eshazen/epic-hours/parts/3digit_screenshot.png

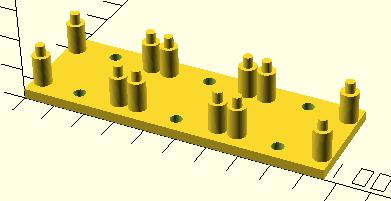
parts/3digit_screenshot.png
