eshazen/epic-hours/parts/#arduino_box_all.dxf

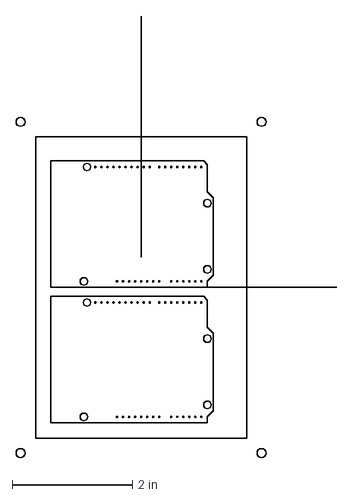
[picture p22: CAD file, 2024-07-11]
parts/#arduino_box_all.dxf
5.33 x 7.33 in
