eshazen/epic-hours/parts/rpi_model/Female USB Type C Connector, RPi4ModelB.SLDPRT

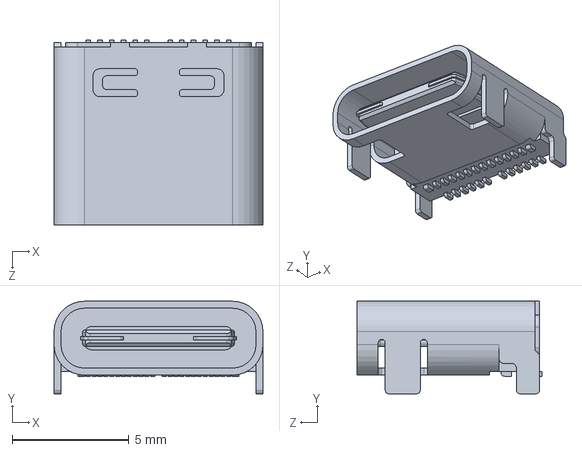
[picture p23: CAD file, 2025-08-05]
parts/rpi_model/Female USB Type C Connector, RPi4ModelB.SLDPRT
8.94 x 3.96 x 7.90 mm
