eshazen/epic-hours/Sketches/cut_back_holes.dxf

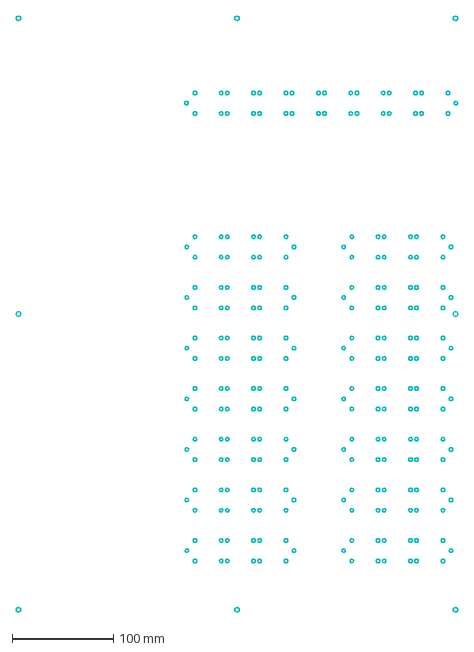
[picture p24: CAD file, 2024-03-23]
Sketches/cut_back_holes.dxf
436.3 x 588.7 mm
