eshazen/epic-hours/parts/arduino_box_cutout.dxf

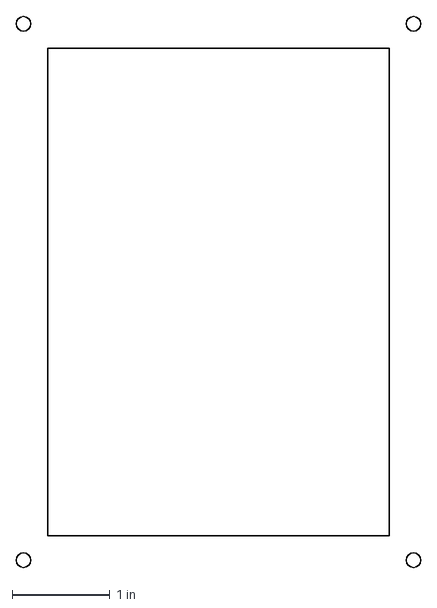
[picture p25: CAD file, 2024-07-11]
parts/arduino_box_cutout.dxf
4.15 x 5.65 in
