eshazen/epic-hours/Sketches/layout_8x8.dxf

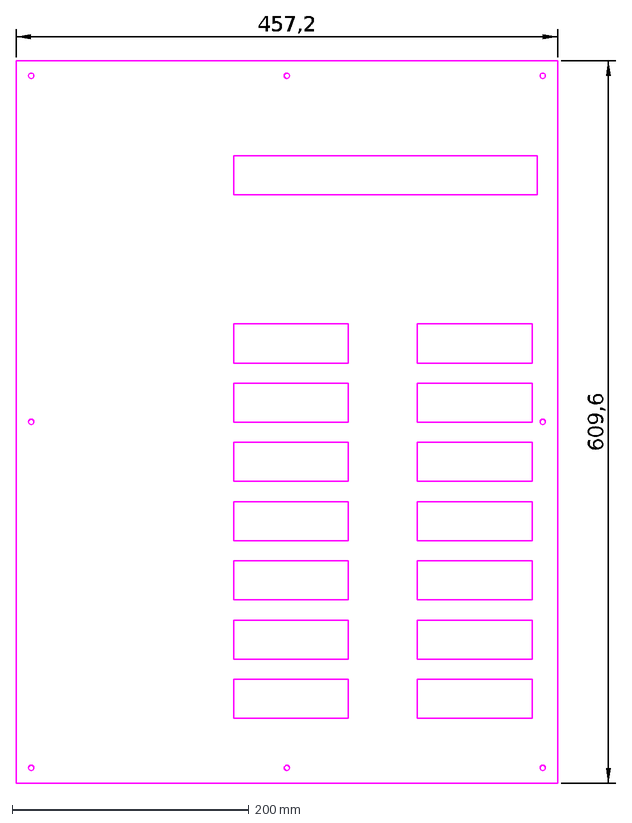
[picture p27: CAD file, 2024-03-07]
Sketches/layout_8x8.dxf
457,2
609,6
