eshazen/epic-hours/parts/arduino_box.stl

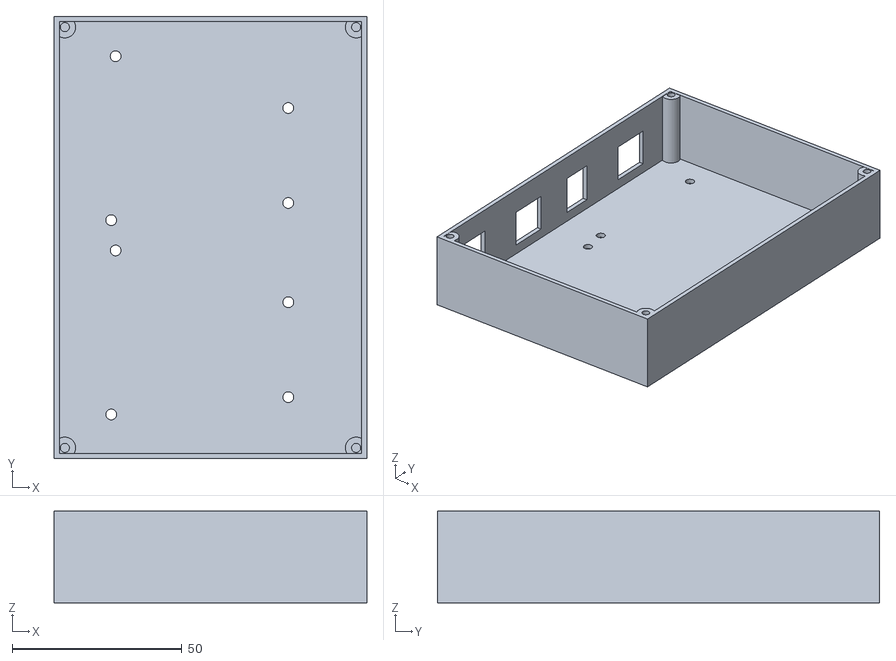
[picture p28: CAD file, 2024-07-11]
parts/arduino_box.stl
92.1 x 130.2 x 27.0
