eshazen/epic-hours/parts/rpi_model/2X USB3.0 PORTS, RPi4ModelB.SLDPRT

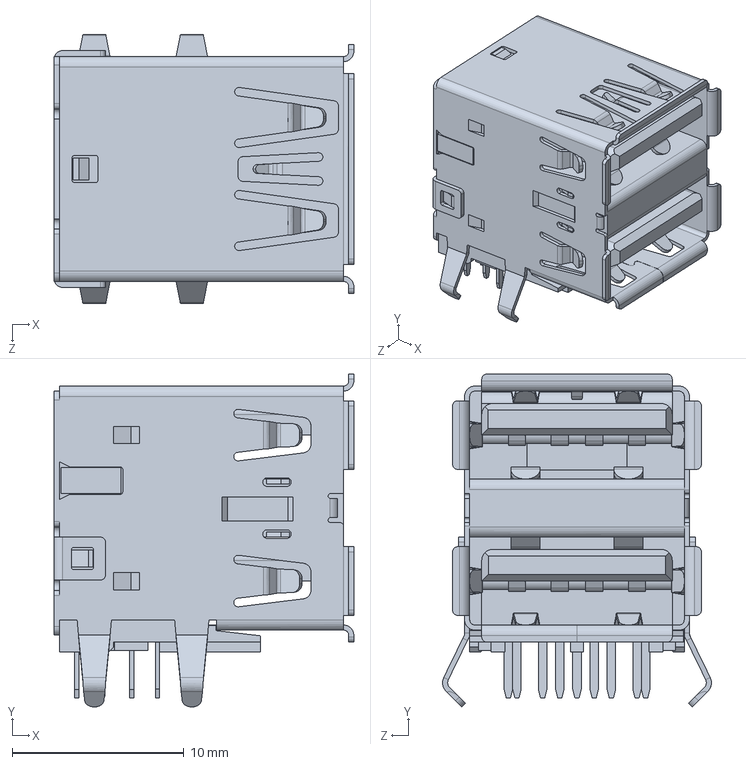
[picture p29: CAD file, 2025-08-05]
parts/rpi_model/2X USB3.0 PORTS, RPi4ModelB.SLDPRT
17.5 x 19.4 x 15.7 mm
