eshazen/epic-hours/Sketches/front_panel.dxf

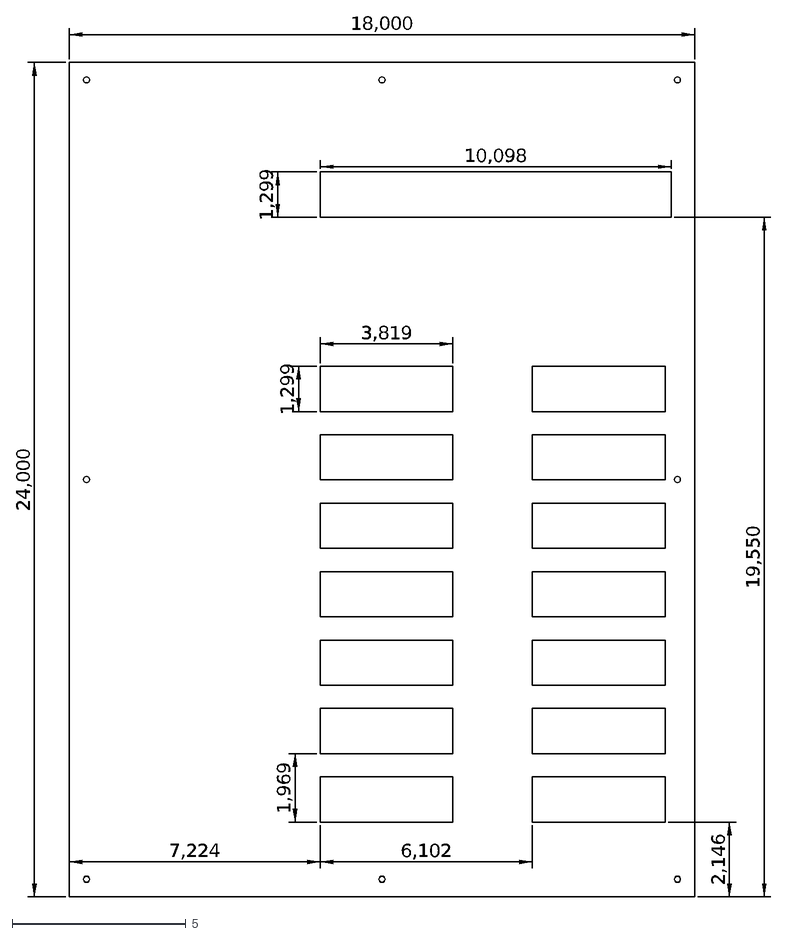
[picture p30: CAD file, 2024-03-07]
Sketches/front_panel.dxf
18,000
3,819
1,299
1,969
6,102
7,224
2,146
24,000
19,550
10,098
