eshazen/epic-hours/parts/arduino_outline.dxf

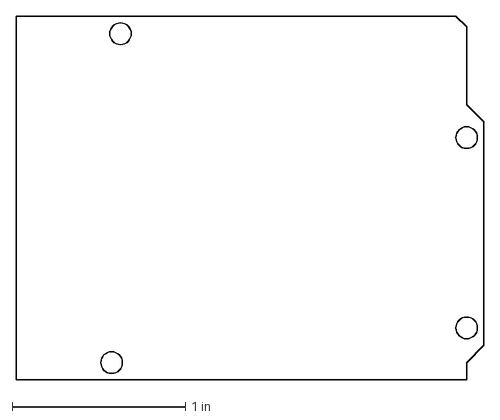
[picture p31: CAD file, 2024-07-11]
parts/arduino_outline.dxf
2.70 x 2.10 in
