eshazen/epic-hours/parts/rpi_model/VIA VL805 PCIe USB 3.0 controller, RPi4ModelB.SLDPRT

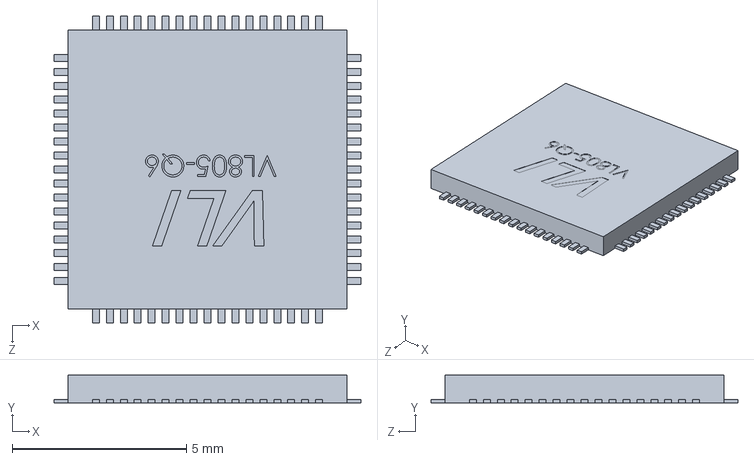
[picture p32: CAD file, 2025-08-05]
parts/rpi_model/VIA VL805 PCIe USB 3.0 controller, RPi4ModelB.SLDPRT
8.80 x 0.8 x 8.80 mm
