eshazen/epic-hours/Sketches/7seg_digit.dxf

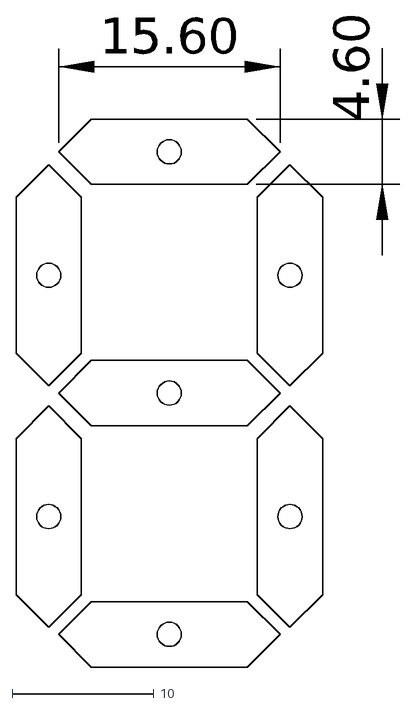
[picture p33: CAD file, 2024-02-12]
Sketches/7seg_digit.dxf
15.60
4.60
