eshazen/epic-hours/parts/8display_standoffs.stl

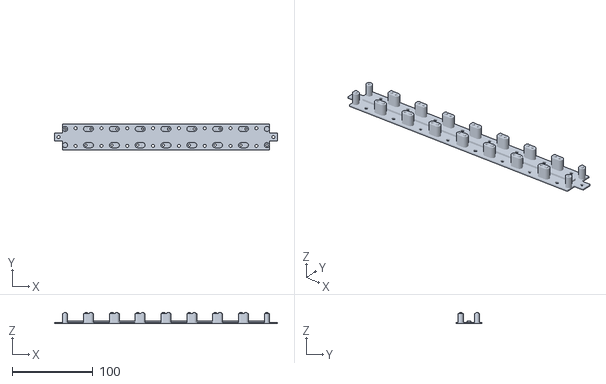
[picture p34: CAD file, 2024-05-08]
parts/8display_standoffs.stl
276.3 x 32.1 x 14.2
