eshazen/epic-hours/parts/rpi_model/2X USB2.0 PORTS, RPi4ModelB.SLDPRT

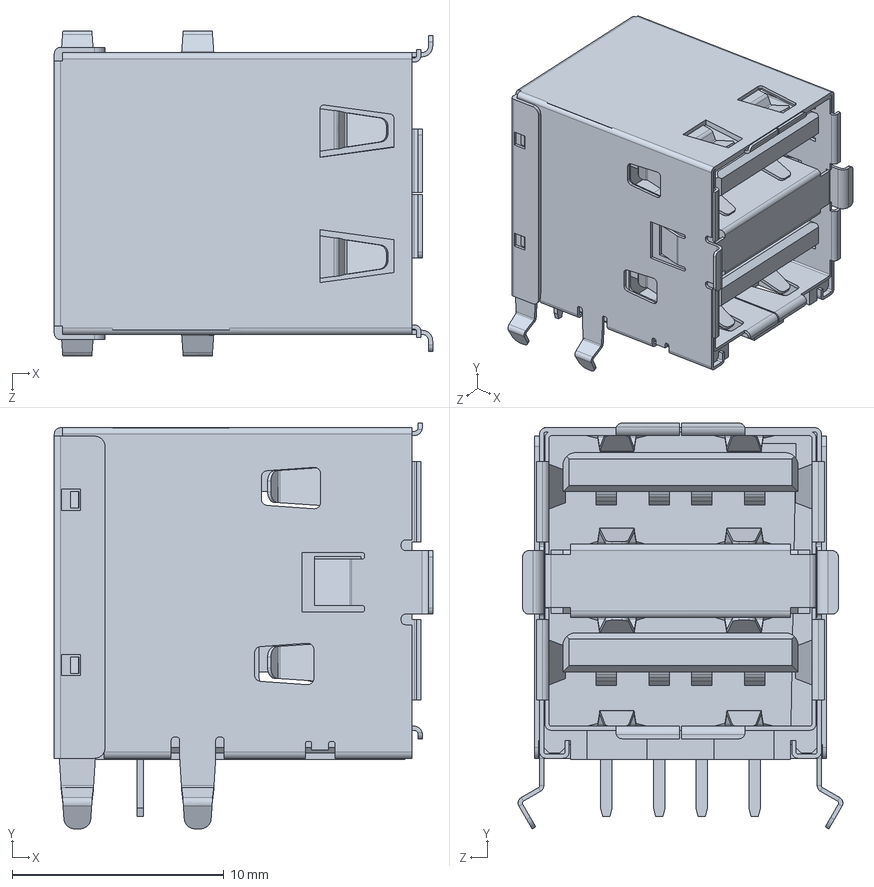
[picture p35: CAD file, 2025-08-05]
parts/rpi_model/2X USB2.0 PORTS, RPi4ModelB.SLDPRT
17.9 x 19.2 x 15.3 mm
