eshazen/epic-hours/parts/display_standoffs.stl

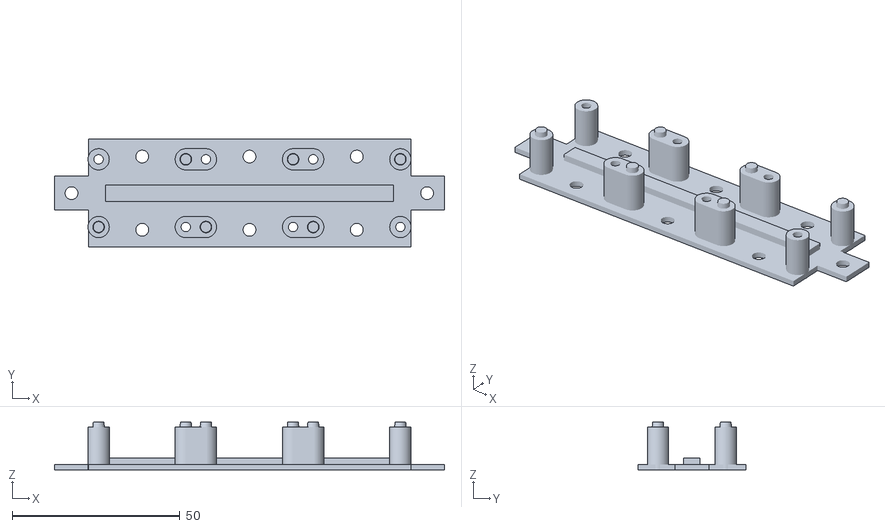
[picture p36: CAD file, 2024-04-19]
parts/display_standoffs.stl
116.3 x 32.1 x 14.2
