eshazen/epic-hours/parts/rpi_model/Cypress CYW43455 Wireless Module Cover, RPi4ModelB.SLDPRT

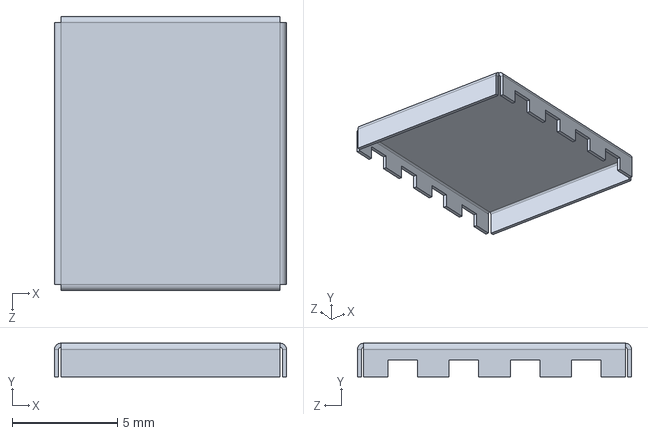
[picture p37: CAD file, 2025-08-05]
parts/rpi_model/Cypress CYW43455 Wireless Module Cover, RPi4ModelB.SLDPRT
11.0 x 1.60 x 13.0 mm
