eshazen/epic-hours/parts/post.stl

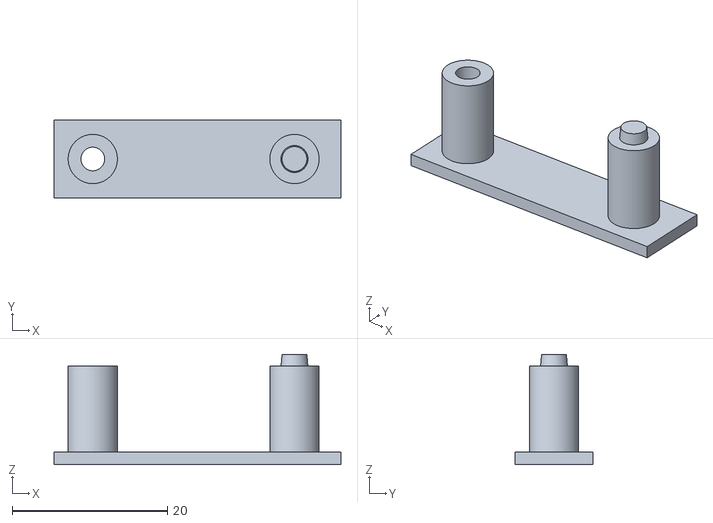
[picture p38: CAD file, 2024-03-23]
parts/post.stl
37.0 x 10.0 x 14.2
