eshazen/epic-hours/parts/display_standoffs_8x.dxf

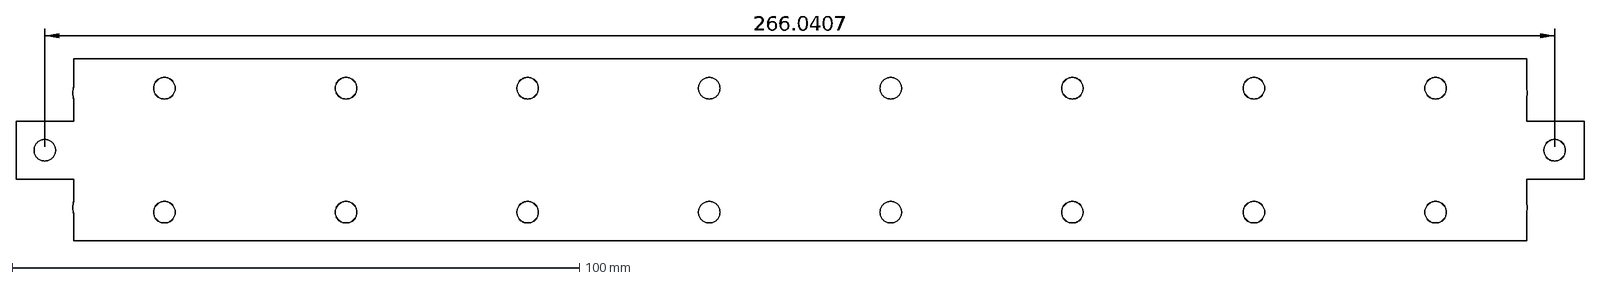
[picture p39: CAD file, 2024-03-23]
parts/display_standoffs_8x.dxf
266.0407
