eshazen/epic-hours/parts/display_standoffs_side.dxf

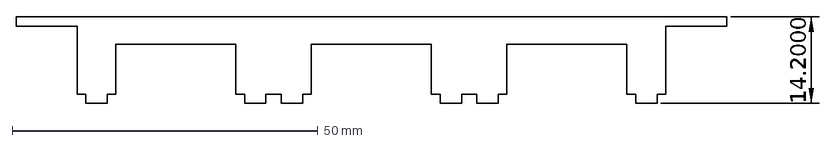
[picture p40: CAD file, 2024-03-23]
parts/display_standoffs_side.dxf
14.2000
