eshazen/epic-hours/parts/display_support.stl

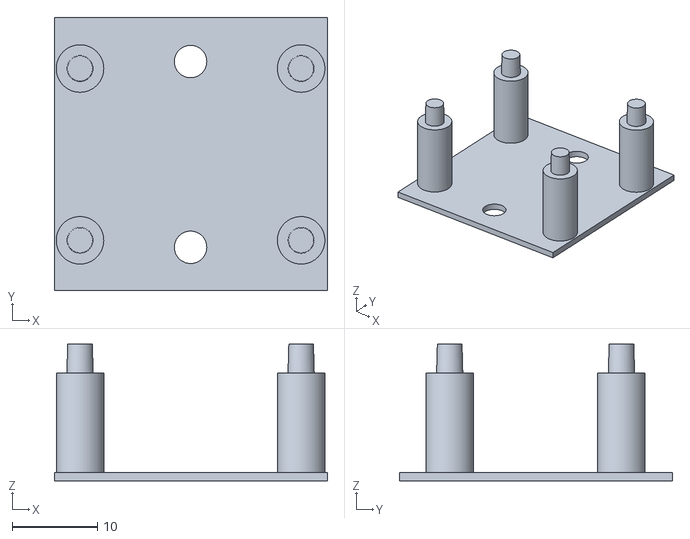
[picture p41: CAD file, 2024-03-11]
parts/display_support.stl
32.1 x 32.1 x 16.1
