eshazen/epic-hours/parts/post.scad

//
// support post with hole and optional lip

tip_dia1 = 3.5;			/* mounting hole ID */
tip_dia2 = 3.2;
tip_hgt = 1.6;			/* length of tip through hole */

peg_dia = 0.25*mm;		/* diameter of peg PCB rests on */
peg_hgt = 0.25*mm;

// support post
module post_at( x, y, lip) {
     translate( [x, y, 0]) {
	  cylinder( h=total_hgt, d=peg_dia);
	  if( lip == 1) {
	    translate( [0, 0, total_hgt-e])
	      cylinder( h=tip_hgt, d1=tip_dia1, d2=tip_dia2);
	  }
     }
}
